Anplus/In-concrete-Backscatter/PCB/SIMU/IC-matching.asc

C1: cap; 10µ
C2: cap; 100µ; V=6.3V
C3: cap; 1µ
C4: cap; 4.7µ
C5: cap; 1µ
C6: cap; 1µ
C7: cap; 1µ
C8: cap; 1µ
C9: cap; 310p
D1: diode
D2: diode
D3: diode
D4: diode
L1: ind; 22µ; Ipk=0.75 Rser=0.19
L2: ind; 1.5m
Rload: res; 500K
U1: LTC3588-1
V1: voltage; SINE(0 1 230000); Rser=100 Cpar=530p
Named nets: 0, out, input
.tran 10 startup
Notes:
  If the simulation model is not found please update with the "Sync Release" command from the "Tools" menu.
  It remains the customer's responsibility to verify proper and reliable operation in the actual application.
  Component substitution and printed circuit board layout may significantly affect circuit performance or reliability.
  Contact your local sales representative for assistance. This circuit is distributed to customers only for use with LTC parts.
  Copyright © 2010 Linear Technology Inc. All rights reserved.
LTC3588-1,  Piezoelectric Energy Harvesting Power Supply with Simulated Remote Sensor/Transmitter
Input: 24V 41Hz  Rs=119K     Output: 3.3V with 30mA 10msec Pulse Load
Piezoelectric Device
MIDE V22BL
1.4 Gpk Force at 41Hz
with Tip Mass of 1 gm.
